papalino456/RobotArm/Gallery/Photo2.jpeg

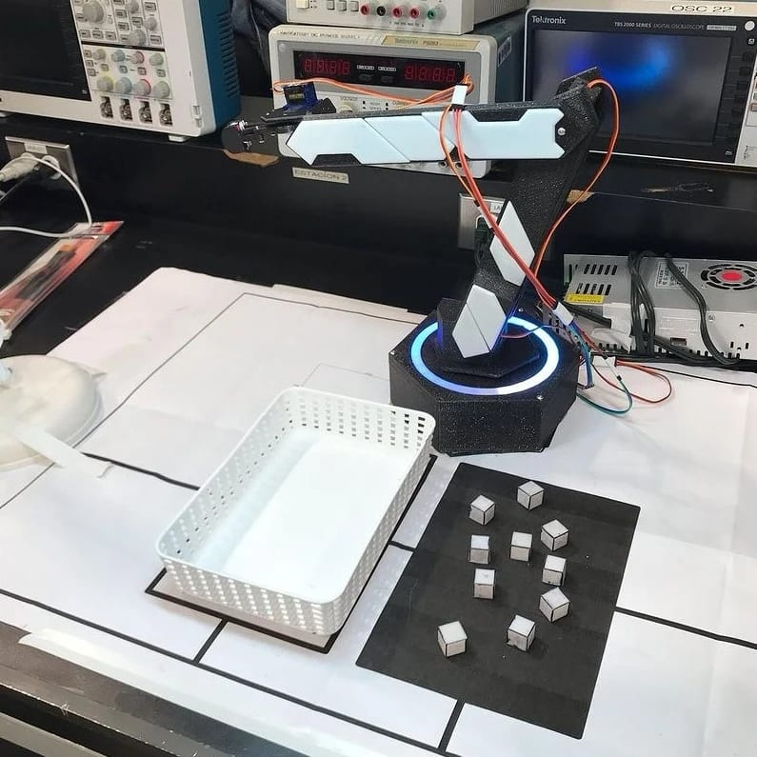
Gallery/Photo2.jpeg
