papalino456/RobotArm/Gallery/Photo3.jpeg

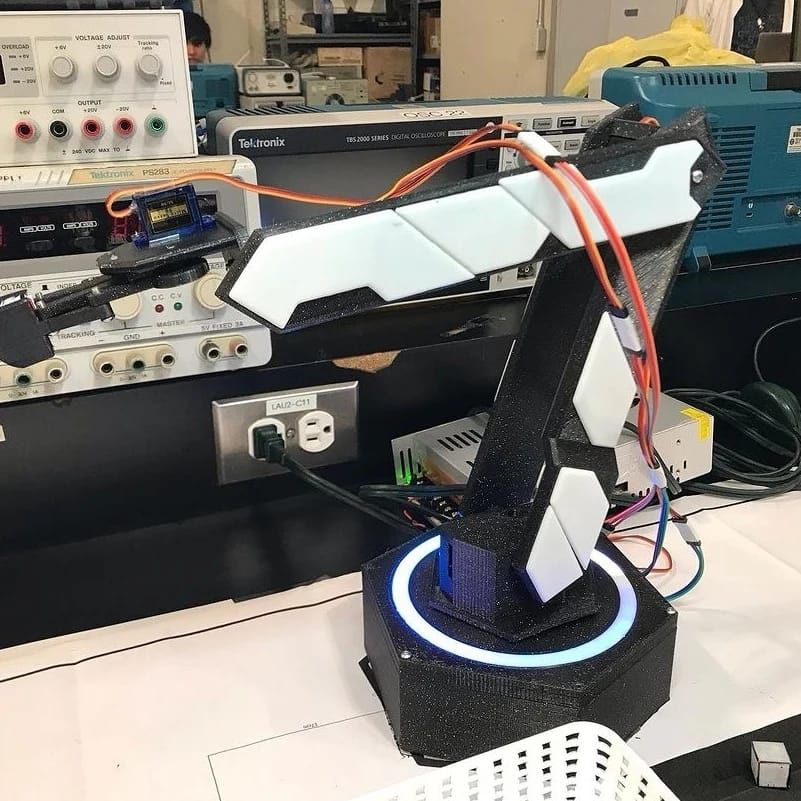
Gallery/Photo3.jpeg
