papalino456/RobotArm/Gallery/Photo4.jpeg

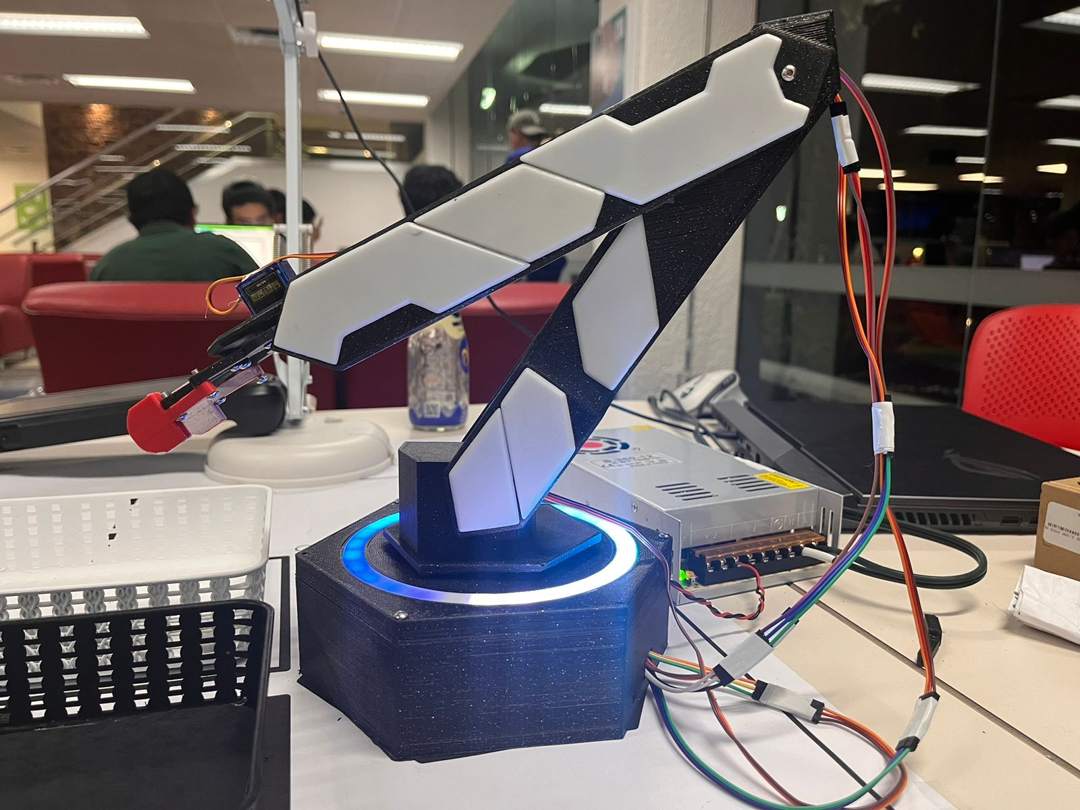
Gallery/Photo4.jpeg
