papalino456/RobotArm/ROBOTARM_STL/Link1_2.stl

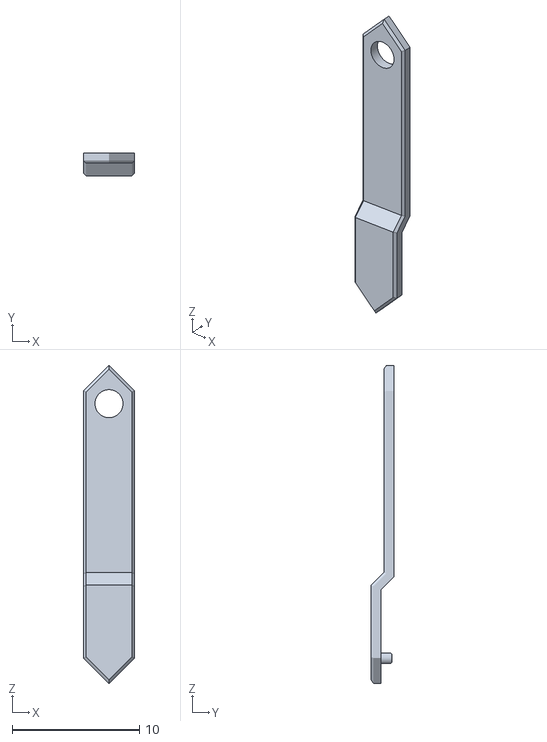
[picture p35: CAD file, 2024-03-07]
ROBOTARM_STL/Link1_2.stl
4.00 x 1.80 x 25.0
